vovets/sonic_beacon/board/output/sonic_beacon-pan-dim.tif

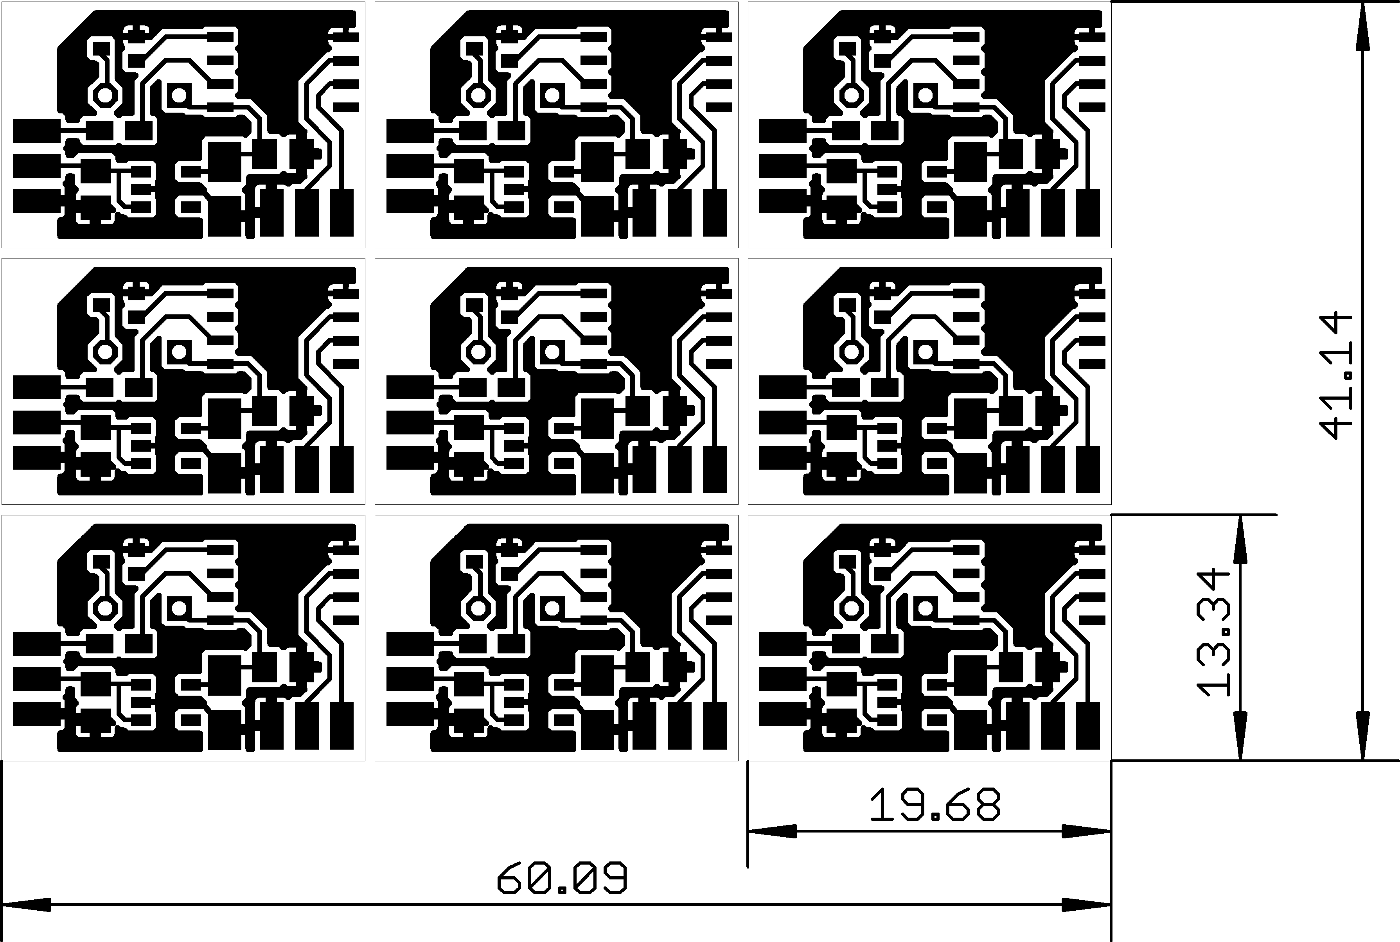
board/output/sonic_beacon-pan-dim.tif
