vovets/sonic_beacon/board/output/sonic_beacon-pan-inv.tif

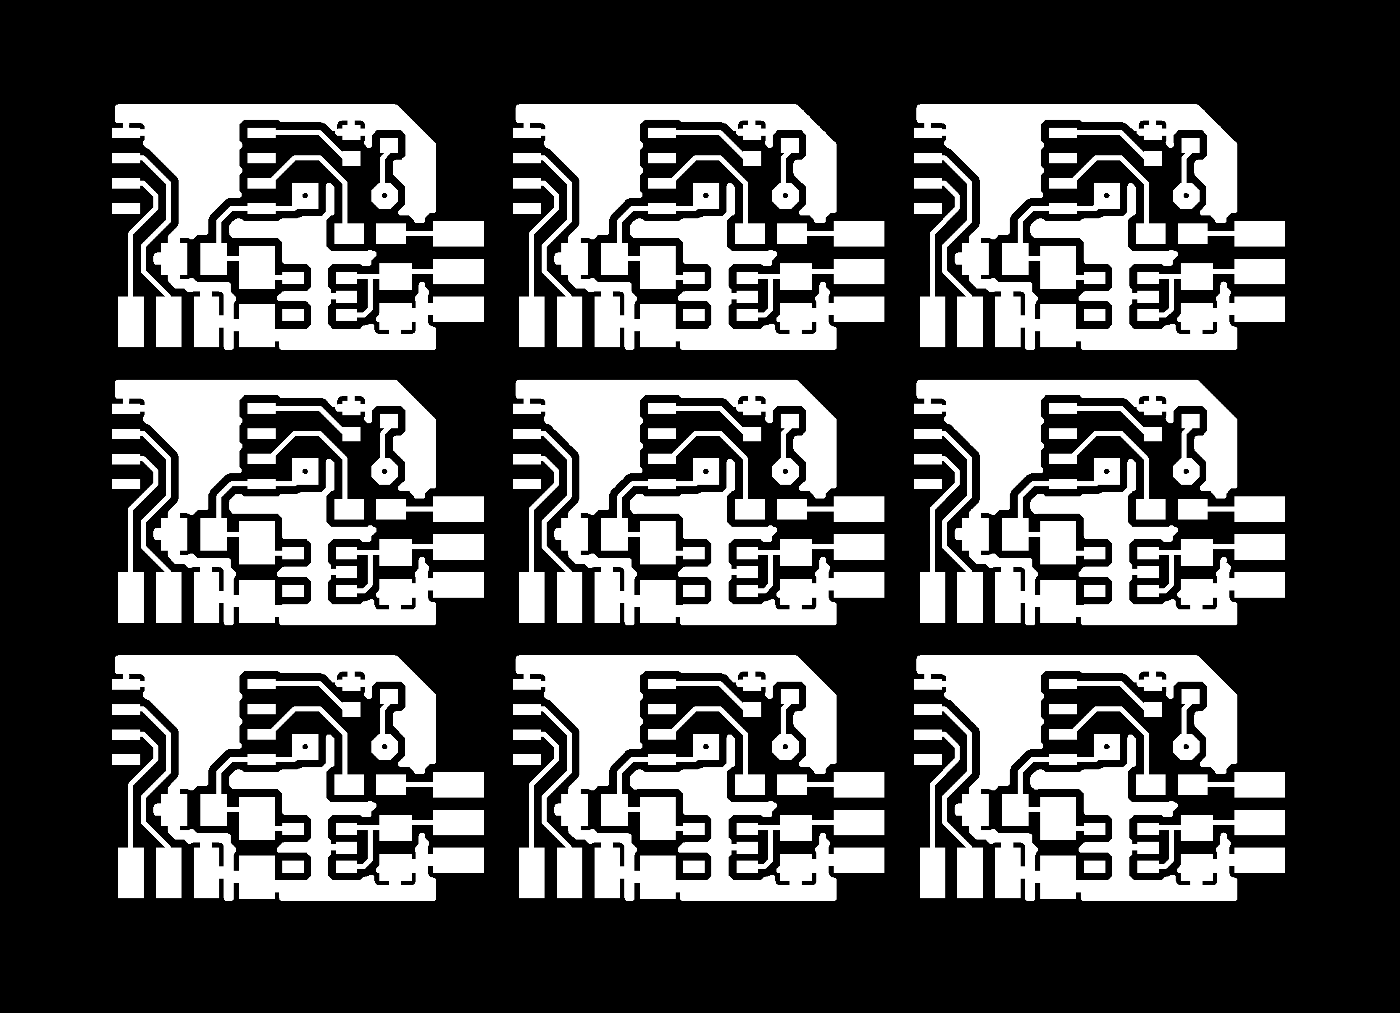
board/output/sonic_beacon-pan-inv.tif
