vovets/sonic_beacon/board/output/sonic_beacon-pan.tif

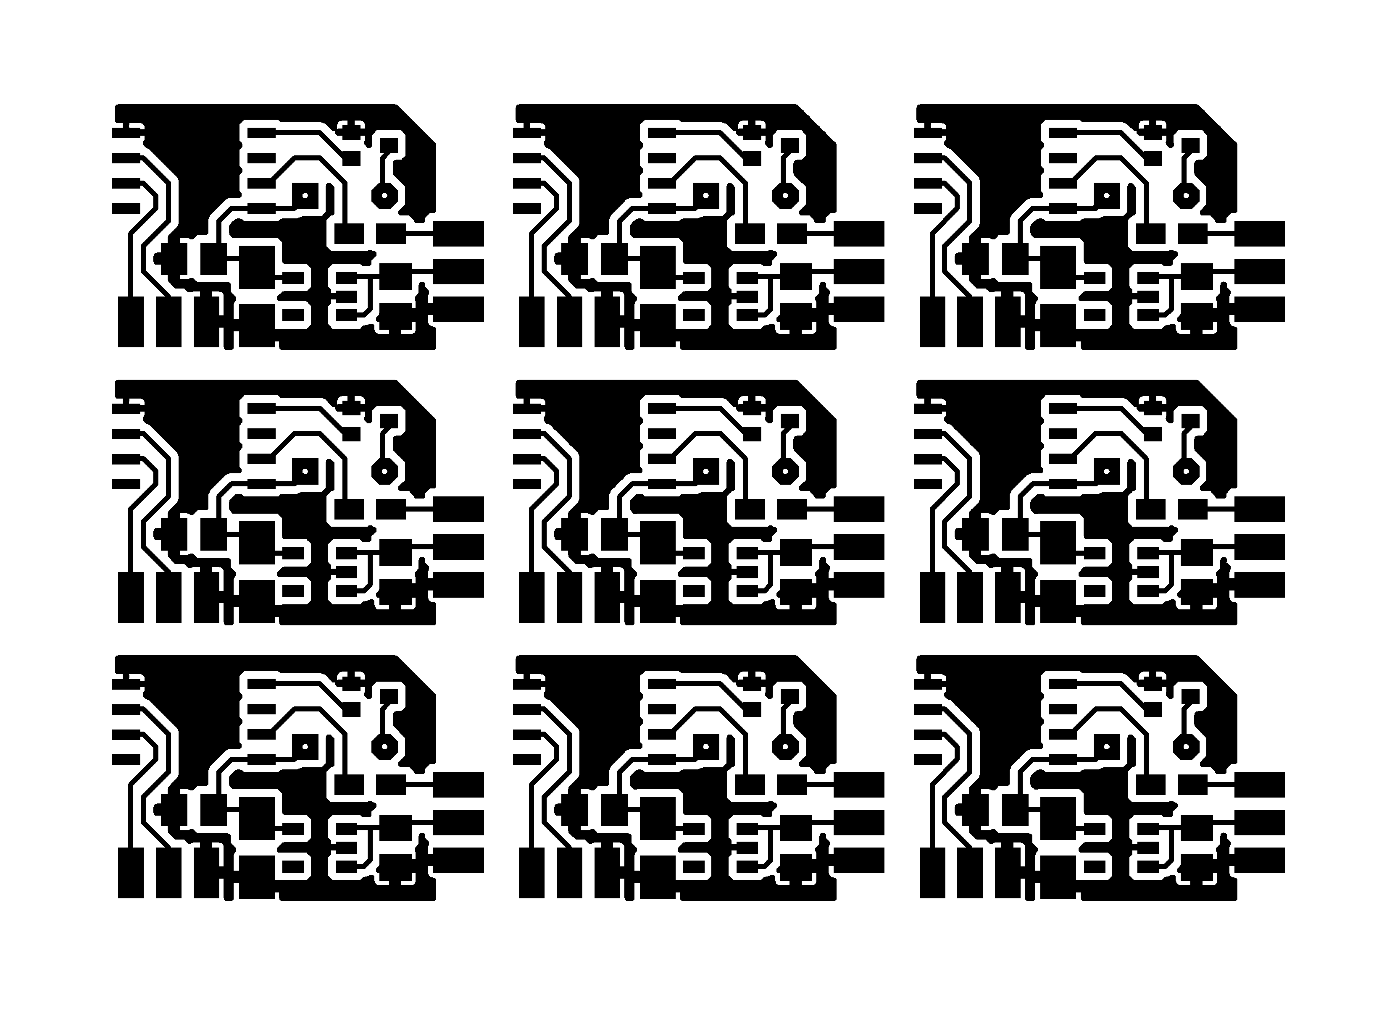
board/output/sonic_beacon-pan.tif
