vovets/sonic_beacon/board/output/top-stop-pan.tif

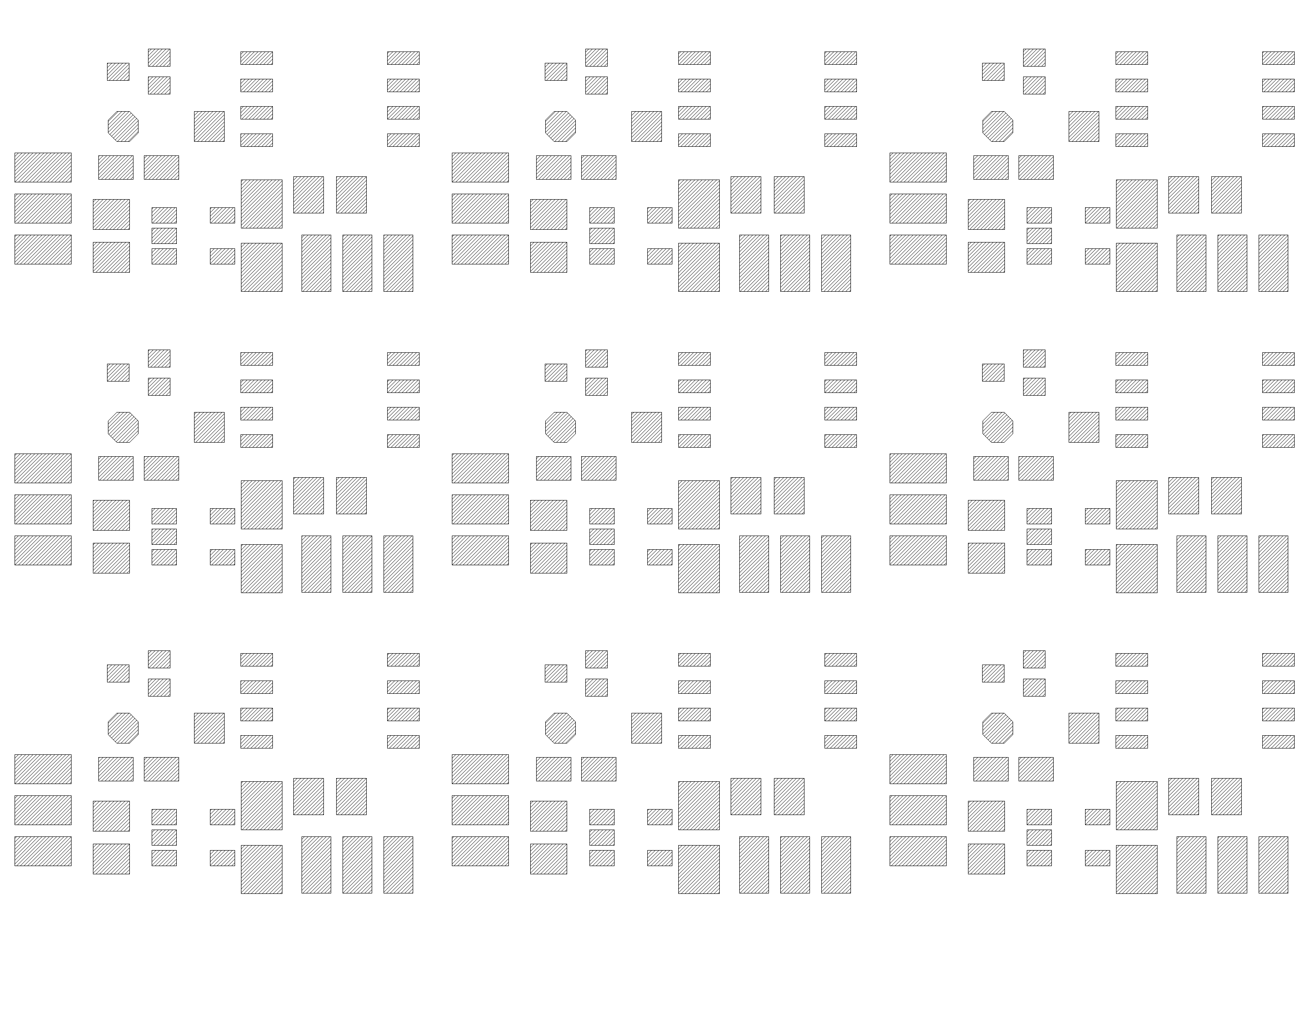
board/output/top-stop-pan.tif
